exddc/virtualchime/chime/src/webd/web_server.cpp

#include "chime/webd_web_server.h"

#include <algorithm>
#include <array>
#include <cctype>
#include <cerrno>
#include <chrono>
#include <cstdio>
#include <cstring>
#include <ctime>
#include <filesystem>
#include <fstream>
#include <map>
#include <optional>
#include <set>
#include <sstream>
#include <string>
#include <utility>
#include <vector>

#include <arpa/inet.h>
#include <fcntl.h>
#include <netinet/in.h>
#include <sys/socket.h>
#include <sys/stat.h>
#include <unistd.h>

#include <openssl/bn.h>
#include <openssl/err.h>
#include <openssl/pem.h>
#include <openssl/ssl.h>
#include <openssl/x509.h>

#include "chime/webd_apply_manager.h"
#include "chime/webd_config_store.h"
#include "chime/webd_json.h"
#include "chime/webd_string_utils.h"
#include "chime/webd_ui_assets.h"
#include "chime/webd_wifi_scan.h"
#include "vc/config/kv_config.h"
#include "vc/logging/logger.h"

namespace chime::webd {
namespace {

constexpr std::size_t kMaxRequestBytes = 65536;
constexpr std::size_t kMaxBodyBytes = 2 * 1024 * 1024;
constexpr const char *kDefaultRingSoundName = "ring-default.wav";
constexpr const char *kReleaseInfoPath = "/etc/virtualchime-release";
constexpr const char *kAppVersionPath = "/etc/chime-app-version";

bool StartsWith(const std::string &value, const std::string &prefix) {
    return value.size() >= prefix.size() && value.compare(0, prefix.size(), prefix) == 0;
}

std::string MimeTypeOnly(const std::string &content_type) {
    const std::size_t semicolon = content_type.find(';');
    const std::string raw = semicolon == std::string::npos ? content_type : content_type.substr(0, semicolon);
    return ToLower(vc::config::trim(raw));
}

bool IsSafeRelativePath(const std::filesystem::path &path) {
    for (const auto &part : path) {
        if (part == "..") {
            return false;
        }
    }
    return true;
}

bool IsSafeSoundName(const std::string &file_name) {
    if (file_name.empty() || file_name.size() > 128) {
        return false;
    }
    if (file_name.find('/') != std::string::npos || file_name.find('\\') != std::string::npos) {
        return false;
    }
    if (file_name.find("..") != std::string::npos) {
        return false;
    }
    const std::string lowered = ToLower(file_name);
    if (!StartsWith(lowered, "ring-") || lowered.rfind(".wav") != lowered.size() - 4) {
        return false;
    }
    for (const char c : file_name) {
        if (!(std::isalnum(static_cast<unsigned char>(c)) || c == '.' || c == '-' || c == '_')) {
            return false;
        }
    }
    return true;
}

bool EnsureDirectoryExists(const std::string &path, std::string *error) {
    std::error_code ec;
    const bool exists = std::filesystem::exists(path, ec);
    if (ec) {
        if (error != nullptr) {
            *error = "exists(" + path + ") failed: " + ec.message();
        }
        return false;
    }

    if (exists) {
        const bool is_directory = std::filesystem::is_directory(path, ec);
        if (ec) {
            if (error != nullptr) {
                *error = "is_directory(" + path + ") failed: " + ec.message();
            }
            return false;
        }
        if (!is_directory) {
            if (error != nullptr) {
                *error = "path exists but is not a directory: " + path;
            }
            return false;
        }
        return true;
    }

    const bool created = std::filesystem::create_directories(path, ec);
    if (ec) {
        if (error != nullptr) {
            *error = "create_directories(" + path + ") failed: " + ec.message();
        }
        return false;
    }

    (void)created;
    return true;
}

void TrySeedDefaultRingSound(const std::string &ring_sounds_dir, const std::string &active_ring_sound_path,
                             vc::logging::Logger &logger) {
    std::error_code ec;
    const std::filesystem::path source_path(active_ring_sound_path);
    const std::filesystem::path target_path = std::filesystem::path(ring_sounds_dir) / kDefaultRingSoundName;
    const std::filesystem::path temp_path = target_path.string() + ".tmp";

    if (!std::filesystem::exists(source_path, ec)) {
        return;
    }
    if (ec) {
        logger.Warn("webd", "failed to inspect active ring sound: " + source_path.string() + " error=" + ec.message());
        return;
    }
    if (!std::filesystem::is_regular_file(source_path, ec)) {
        return;
    }
    if (ec) {
        logger.Warn("webd", "failed to inspect active ring sound: " + source_path.string() + " error=" + ec.message());
        return;
    }

    if (std::filesystem::exists(target_path, ec)) {
        return;
    }
    if (ec) {
        logger.Warn("webd",
                    "failed to inspect default ring sound target: " + target_path.string() + " error=" + ec.message());
        return;
    }

    std::filesystem::copy_file(source_path, temp_path, std::filesystem::copy_options::overwrite_existing, ec);
    if (ec) {
        logger.Warn("webd", "failed to seed default ring sound: copy " + source_path.string() + " -> " +
                                temp_path.string() + " error=" + ec.message());
        return;
    }

    std::filesystem::rename(temp_path, target_path, ec);
    if (ec) {
        std::error_code remove_ec;
        std::filesystem::remove(temp_path, remove_ec);
        logger.Warn("webd", "failed to seed default ring sound: rename " + temp_path.string() + " -> " +
                                target_path.string() + " error=" + ec.message());
    }
}

std::string ContentTypeForPath(const std::filesystem::path &path) {
    const std::string extension = ToLower(path.extension().string());
    if (extension == ".html") {
        return "text/html; charset=utf-8";
    }
    if (extension == ".css") {
        return "text/css; charset=utf-8";
    }
    if (extension == ".js") {
        return "application/javascript; charset=utf-8";
    }
    if (extension == ".json") {
        return "application/json; charset=utf-8";
    }
    if (extension == ".svg") {
        return "image/svg+xml";
    }
    if (extension == ".ico") {
        return "image/x-icon";
    }
    if (extension == ".png") {
        return "image/png";
    }
    if (extension == ".jpg" || extension == ".jpeg") {
        return "image/jpeg";
    }
    if (extension == ".webp") {
        return "image/webp";
    }
    if (extension == ".woff2") {
        return "font/woff2";
    }
    if (extension == ".woff") {
        return "font/woff";
    }
    return "application/octet-stream";
}

std::string CacheControlForPath(const std::string &request_path, const std::filesystem::path &path) {
    if (ToLower(path.extension().string()) == ".html") {
        return "no-cache";
    }
    if (StartsWith(request_path, "/assets/")) {
        return "public, max-age=31536000, immutable";
    }
    return "public, max-age=3600";
}

bool ReadFile(const std::filesystem::path &path, std::string *body) {
    if (body == nullptr) {
        return false;
    }
    std::ifstream file(path, std::ios::binary);
    if (!file.is_open()) {
        return false;
    }
    std::ostringstream stream;
    stream << file.rdbuf();
    *body = stream.str();
    return true;
}

std::vector<std::string> ReadObservedTopicsFromFile(const std::string &path, std::string *error) {
    std::vector<std::string> topics;
    std::ifstream file(path);
    if (!file.is_open()) {
        if (std::filesystem::exists(path)) {
            if (error != nullptr) {
                *error = "failed to open observed topics file";
            }
        }
        return topics;
    }

    std::set<std::string> seen;
    std::string line;
    while (std::getline(file, line)) {
        const std::string topic = vc::config::trim(line);
        if (topic.empty()) {
            continue;
        }
        if (seen.insert(topic).second) {
            topics.push_back(topic);
        }
    }
    return topics;
}

std::string ReadTrimmedFirstLine(const std::string &path) {
    std::ifstream file(path);
    if (!file.is_open()) {
        return "";
    }
    std::string line;
    if (!std::getline(file, line)) {
        return "";
    }
    return vc::config::trim(line);
}

std::map<std::string, std::string> ReadKeyValueFile(const std::string &path) {
    std::map<std::string, std::string> values;
    std::ifstream file(path);
    if (!file.is_open()) {
        return values;
    }

    std::string line;
    while (std::getline(file, line)) {
        const std::string trimmed = vc::config::trim(line);
        if (trimmed.empty() || trimmed[0] == '#') {
            continue;
        }

        const std::size_t separator = trimmed.find('=');
        if (separator == std::string::npos) {
            continue;
        }

        const std::string key = vc::config::trim(trimmed.substr(0, separator));
        const std::string value = vc::config::trim(trimmed.substr(separator + 1));
        if (!key.empty()) {
            values[key] = value;
        }
    }

    return values;
}

std::string ReadValueOrDefault(const std::map<std::string, std::string> &values, const std::string &key,
                               const std::string &fallback) {
    const auto it = values.find(key);
    if (it == values.end() || it->second.empty()) {
        return fallback;
    }
    return it->second;
}

std::string StatusText(int code) {
    switch (code) {
    case 200:
        return "OK";
    case 400:
        return "Bad Request";
    case 404:
        return "Not Found";
    case 405:
        return "Method Not Allowed";
    case 500:
        return "Internal Server Error";
    case 501:
        return "Not Implemented";
    case 503:
        return "Service Unavailable";
    default:
        return "Error";
    }
}

bool WriteAllSsl(SSL *ssl, const std::string &data) {
    std::size_t offset = 0;
    while (offset < data.size()) {
        const int written =
            SSL_write(ssl, data.data() + offset, static_cast<int>(std::min<std::size_t>(data.size() - offset, 16384)));
        if (written <= 0) {
            return false;
        }
        offset += static_cast<std::size_t>(written);
    }
    return true;
}

std::optional<std::string> ReadRequiredString(const JsonValue &object, const std::string &key,
                                              std::vector<ValidationError> *errors) {
    const auto field = GetObjectField(object, key);
    if (!field.has_value()) {
        if (errors != nullptr) {
            errors->push_back({key, key + " is required"});
        }
        return std::nullopt;
    }

    std::string value;
    if (!field->AsString(&value)) {
        if (errors != nullptr) {
            errors->push_back({key, key + " must be a string"});
        }
        return std::nullopt;
    }

    return value;
}

std::optional<int> ReadRequiredInt(const JsonValue &object, const std::string &key,
                                   std::vector<ValidationError> *errors) {
    const auto field = GetObjectField(object, key);
    if (!field.has_value()) {
        if (errors != nullptr) {
            errors->push_back({key, key + " is required"});
        }
        return std::nullopt;
    }

    double value = 0.0;
    if (!field->AsNumber(&value)) {
        if (errors != nullptr) {
            errors->push_back({key, key + " must be a number"});
        }
        return std::nullopt;
    }

    const int rounded = static_cast<int>(value);
    if (static_cast<double>(rounded) != value) {
        if (errors != nullptr) {
            errors->push_back({key, key + " must be an integer"});
        }
        return std::nullopt;
    }

    return rounded;
}

std::optional<bool> ReadRequiredBool(const JsonValue &object, const std::string &key,
                                     std::vector<ValidationError> *errors) {
    const auto field = GetObjectField(object, key);
    if (!field.has_value()) {
        if (errors != nullptr) {
            errors->push_back({key, key + " is required"});
        }
        return std::nullopt;
    }

    bool value = false;
    if (!field->AsBool(&value)) {
        if (errors != nullptr) {
            errors->push_back({key, key + " must be a boolean"});
        }
        return std::nullopt;
    }

    return value;
}

std::optional<std::vector<std::string>> ReadRequiredStringArray(const JsonValue &object, const std::string &key,
                                                                std::vector<ValidationError> *errors) {
    const auto field = GetObjectField(object, key);
    if (!field.has_value()) {
        if (errors != nullptr) {
            errors->push_back({key, key + " is required"});
        }
        return std::nullopt;
    }

    std::vector<JsonValue> items;
    if (!field->AsArray(&items)) {
        if (errors != nullptr) {
            errors->push_back({key, key + " must be an array"});
        }
        return std::nullopt;
    }

    std::vector<std::string> output;
    output.reserve(items.size());
    for (std::size_t i = 0; i < items.size(); ++i) {
        std::string entry;
        if (!items[i].AsString(&entry)) {
            if (errors != nullptr) {
                errors->push_back({key, key + "[" + std::to_string(i) + "] must be a string"});
            }
            continue;
        }
        output.push_back(entry);
    }

    return output;
}

std::optional<std::string> ReadOptionalString(const JsonValue &object, const std::string &key,
                                              std::vector<ValidationError> *errors) {
    const auto field = GetObjectField(object, key);
    if (!field.has_value()) {
        return std::nullopt;
    }

    std::string value;
    if (!field->AsString(&value)) {
        if (errors != nullptr) {
            errors->push_back({key, key + " must be a string"});
        }
        return std::nullopt;
    }

    return value;
}

std::string SerializeValidationErrors(const std::vector<ValidationError> &validation_errors) {
    std::string body = "[";
    for (std::size_t i = 0; i < validation_errors.size(); ++i) {
        if (i > 0) {
            body += ",";
        }
        body += "{";
        body += "\"field\":" + JsonString(validation_errors[i].field) + ",";
        body += "\"message\":" + JsonString(validation_errors[i].message);
        body += "}";
    }
    body += "]";
    return body;
}

std::string SerializeTopics(const std::vector<std::string> &topics) {
    std::string output = "[";
    for (std::size_t i = 0; i < topics.size(); ++i) {
        if (i > 0) {
            output += ",";
        }
        output += JsonString(topics[i]);
    }
    output += "]";
    return output;
}

std::string SerializeApplyStatus(const ApplyStatus &status) {
    std::string output = "{";
    output += "\"job_id\":" + std::to_string(status.job_id) + ",";
    output += "\"state\":" + JsonString(status.state) + ",";
    output += "\"started_at_utc\":" + JsonString(status.started_at_utc) + ",";
    output += "\"finished_at_utc\":" + JsonString(status.finished_at_utc) + ",";
    output += "\"error\":" + JsonString(status.error);
    output += "}";
    return output;
}

bool GenerateSelfSignedCertificate(const std::string &cert_path, const std::string &key_path, std::string *error) {
    EVP_PKEY *pkey = EVP_PKEY_new();
    if (pkey == nullptr) {
        if (error != nullptr) {
            *error = "EVP_PKEY_new failed";
        }
        return false;
    }

    RSA *rsa = RSA_new();
    BIGNUM *exponent = BN_new();
    X509 *cert = nullptr;
    X509_NAME *name = nullptr;
    FILE *key_file = nullptr;
    FILE *cert_file = nullptr;

    bool success = false;

    if (rsa == nullptr || exponent == nullptr) {
        if (error != nullptr) {
            *error = "RSA allocation failed";
        }
        goto cleanup;
    }

    if (BN_set_word(exponent, RSA_F4) != 1) {
        if (error != nullptr) {
            *error = "BN_set_word failed";
        }
        goto cleanup;
    }

    if (RSA_generate_key_ex(rsa, 2048, exponent, nullptr) != 1) {
        if (error != nullptr) {
            *error = "RSA_generate_key_ex failed";
        }
        goto cleanup;
    }

    if (EVP_PKEY_assign_RSA(pkey, rsa) != 1) {
        if (error != nullptr) {
            *error = "EVP_PKEY_assign_RSA failed";
        }
        goto cleanup;
    }
    rsa = nullptr;

    cert = X509_new();
    if (cert == nullptr) {
        if (error != nullptr) {
            *error = "X509_new failed";
        }
        goto cleanup;
    }

    X509_set_version(cert, 2);
    ASN1_INTEGER_set(X509_get_serialNumber(cert), static_cast<long>(time(nullptr)));
    X509_gmtime_adj(X509_get_notBefore(cert), 0);
    X509_gmtime_adj(X509_get_notAfter(cert), 60L * 60L * 24L * 365L * 10L);
    X509_set_pubkey(cert, pkey);

    name = X509_get_subject_name(cert);
    X509_NAME_add_entry_by_txt(name, "C", MBSTRING_ASC, reinterpret_cast<const unsigned char *>("US"), -1, -1, 0);
    X509_NAME_add_entry_by_txt(name, "O", MBSTRING_ASC, reinterpret_cast<const unsigned char *>("VirtualChime"), -1, -1,
                               0);
    X509_NAME_add_entry_by_txt(name, "CN", MBSTRING_ASC, reinterpret_cast<const unsigned char *>("chime.local"), -1, -1,
                               0);
    X509_set_issuer_name(cert, name);

    if (X509_sign(cert, pkey, EVP_sha256()) == 0) {
        if (error != nullptr) {
            *error = "X509_sign failed";
        }
        goto cleanup;
    }

    key_file = fopen(key_path.c_str(), "w");
    if (key_file == nullptr) {
        if (error != nullptr) {
            *error = "failed to open key file";
        }
        goto cleanup;
    }
    if (PEM_write_PrivateKey(key_file, pkey, nullptr, nullptr, 0, nullptr, nullptr) != 1) {
        if (error != nullptr) {
            *error = "PEM_write_PrivateKey failed";
        }
        goto cleanup;
    }

    cert_file = fopen(cert_path.c_str(), "w");
    if (cert_file == nullptr) {
        if (error != nullptr) {
            *error = "failed to open cert file";
        }
        goto cleanup;
    }
    if (PEM_write_X509(cert_file, cert) != 1) {
        if (error != nullptr) {
            *error = "PEM_write_X509 failed";
        }
        goto cleanup;
    }

    chmod(key_path.c_str(), 0600);
    chmod(cert_path.c_str(), 0644);
    success = true;

cleanup:
    if (key_file != nullptr) {
        fclose(key_file);
    }
    if (cert_file != nullptr) {
        fclose(cert_file);
    }
    if (rsa != nullptr) {
        RSA_free(rsa);
    }
    if (exponent != nullptr) {
        BN_free(exponent);
    }
    if (cert != nullptr) {
        X509_free(cert);
    }
    EVP_PKEY_free(pkey);

    return success;
}

} // namespace

WebServer::WebServer(vc::logging::Logger &logger, ConfigStore &config_store, WifiScanner &wifi_scanner,
                     ApplyManager &apply_manager, std::string bind_address, int port, std::string cert_path,
                     std::string key_path, std::string ui_dist_dir, std::string observed_topics_path,
                     std::string ring_sounds_dir, std::string active_ring_sound_path)
    : logger_(logger), config_store_(config_store), wifi_scanner_(wifi_scanner), apply_manager_(apply_manager),
      bind_address_(std::move(bind_address)), port_(port), cert_path_(std::move(cert_path)),
      key_path_(std::move(key_path)), ui_dist_dir_(std::move(ui_dist_dir)),
      observed_topics_path_(std::move(observed_topics_path)), ring_sounds_dir_(std::move(ring_sounds_dir)),
      active_ring_sound_path_(std::move(active_ring_sound_path)) {}

WebServer::~WebServer() {
    Stop();
}

bool WebServer::Start() {
    if (running_.load()) {
        return true;
    }

    std::string error;
    if (!EnsureTlsMaterial(&error)) {
        logger_.Error("webd", "TLS setup failed: " + error);
        return false;
    }

    SSL_load_error_strings();
    OpenSSL_add_ssl_algorithms();

    SSL_CTX *ctx = SSL_CTX_new(TLS_server_method());
    if (ctx == nullptr) {
        logger_.Error("webd", "SSL_CTX_new failed");
        return false;
    }

    SSL_CTX_set_min_proto_version(ctx, TLS1_2_VERSION);

    if (SSL_CTX_use_certificate_file(ctx, cert_path_.c_str(), SSL_FILETYPE_PEM) != 1) {
        logger_.Error("webd", "failed to load TLS certificate from " + cert_path_);
        SSL_CTX_free(ctx);
        return false;
    }

    if (SSL_CTX_use_PrivateKey_file(ctx, key_path_.c_str(), SSL_FILETYPE_PEM) != 1) {
        logger_.Error("webd", "failed to load TLS private key from " + key_path_);
        SSL_CTX_free(ctx);
        return false;
    }

    listen_fd_ = socket(AF_INET, SOCK_STREAM, 0);
    if (listen_fd_ < 0) {
        logger_.Error("webd", "socket() failed");
        SSL_CTX_free(ctx);
        return false;
    }

    const int reuse = 1;
    setsockopt(listen_fd_, SOL_SOCKET, SO_REUSEADDR, &reuse, sizeof(reuse));

    struct sockaddr_in address{};
    address.sin_family = AF_INET;
    address.sin_port = htons(static_cast<uint16_t>(port_));
    if (inet_pton(AF_INET, bind_address_.c_str(), &address.sin_addr) != 1) {
        logger_.Error("webd", "invalid bind address: " + bind_address_);
        close(listen_fd_);
        listen_fd_ = -1;
        SSL_CTX_free(ctx);
        return false;
    }

    if (bind(listen_fd_, reinterpret_cast<struct sockaddr *>(&address), sizeof(address)) != 0) {
        logger_.Error("webd", "bind() failed on " + bind_address_ + ":" + std::to_string(port_));
        close(listen_fd_);
        listen_fd_ = -1;
        SSL_CTX_free(ctx);
        return false;
    }

    if (listen(listen_fd_, 16) != 0) {
        logger_.Error("webd", "listen() failed");
        close(listen_fd_);
        listen_fd_ = -1;
        SSL_CTX_free(ctx);
        return false;
    }

    ssl_ctx_ = ctx;
    running_.store(true);
    accept_thread_ = std::thread([this]() { AcceptLoop(); });

    logger_.Info("webd", "https server listening on " + bind_address_ + ":" + std::to_string(port_));
    return true;
}

void WebServer::Stop() {
    if (!running_.exchange(false)) {
        return;
    }

    if (listen_fd_ >= 0) {
        shutdown(listen_fd_, SHUT_RDWR);
        close(listen_fd_);
        listen_fd_ = -1;
    }

    if (accept_thread_.joinable()) {
        accept_thread_.join();
    }

    if (ssl_ctx_ != nullptr) {
        SSL_CTX_free(static_cast<SSL_CTX *>(ssl_ctx_));
        ssl_ctx_ = nullptr;
    }

    EVP_cleanup();
}

void WebServer::AcceptLoop() {
    while (running_.load()) {
        struct sockaddr_in client_addr{};
        socklen_t client_len = sizeof(client_addr);
        const int client_fd = accept(listen_fd_, reinterpret_cast<struct sockaddr *>(&client_addr), &client_len);

        if (client_fd < 0) {
            if (errno == EINTR) {
                continue;
            }
            if (!running_.load()) {
                break;
            }
            std::this_thread::sleep_for(std::chrono::milliseconds(50));
            continue;
        }

        HandleConnection(client_fd);
    }
}

void WebServer::HandleConnection(int client_fd) {
    SSL *ssl = SSL_new(static_cast<SSL_CTX *>(ssl_ctx_));
    if (ssl == nullptr) {
        close(client_fd);
        return;
    }

    SSL_set_fd(ssl, client_fd);
    if (SSL_accept(ssl) <= 0) {
        SSL_shutdown(ssl);
        SSL_free(ssl);
        close(client_fd);
        return;
    }

    HttpRequest request;
    std::string read_error;
    HttpResponse response;
    if (!ReadHttpRequest(ssl, &request, &read_error)) {
        response.status = 400;
        response.body = "{\"error\":\"bad_request\",\"message\":" + JsonString(read_error) + "}";
    } else {
        response = Route(request);
    }

    std::string raw;
    raw += "HTTP/1.1 " + std::to_string(response.status) + " " + StatusText(response.status) + "\r\n";
    raw += "Content-Type: " + response.content_type + "\r\n";
    raw += "Content-Length: " + std::to_string(response.body.size()) + "\r\n";
    raw += "Cache-Control: " + response.cache_control + "\r\n";
    raw += "Connection: close\r\n";
    raw += "\r\n";
    raw += response.body;

    WriteAllSsl(ssl, raw);

    SSL_shutdown(ssl);
    SSL_free(ssl);
    close(client_fd);
}

bool WebServer::ReadHttpRequest(void *ssl_ptr, HttpRequest *request, std::string *error) const {
    if (ssl_ptr == nullptr || request == nullptr || error == nullptr) {
        return false;
    }

    SSL *ssl = static_cast<SSL *>(ssl_ptr);

    std::string data;
    data.reserve(2048);

    std::size_t headers_end = std::string::npos;
    while (headers_end == std::string::npos) {
        if (data.size() >= kMaxRequestBytes) {
            *error = "request too large";
            return false;
        }

        std::array<char, 2048> buffer{};
        const int bytes = SSL_read(ssl, buffer.data(), static_cast<int>(buffer.size()));
        if (bytes <= 0) {
            *error = "failed to read request";
            return false;
        }

        data.append(buffer.data(), static_cast<std::size_t>(bytes));
        headers_end = data.find("\r\n\r\n");
    }

    const std::string header_blob = data.substr(0, headers_end);
    std::istringstream header_stream(header_blob);

    std::string request_line;
    if (!std::getline(header_stream, request_line)) {
        *error = "missing request line";
        return false;
    }
    if (!request_line.empty() && request_line.back() == '\r') {
        request_line.pop_back();
    }

    std::istringstream request_line_stream(request_line);
    std::string method;
    std::string path;
    std::string version;
    request_line_stream >> method >> path >> version;
    if (method.empty() || path.empty() || version.empty()) {
        *error = "invalid request line";
        return false;
    }

    std::map<std::string, std::string> headers;
    std::string header_line;
    while (std::getline(header_stream, header_line)) {
        if (!header_line.empty() && header_line.back() == '\r') {
            header_line.pop_back();
        }
        const auto sep = header_line.find(':');
        if (sep == std::string::npos) {
            continue;
        }
        const std::string key = ToLower(vc::config::trim(header_line.substr(0, sep)));
        const std::string value = vc::config::trim(header_line.substr(sep + 1));
        headers[key] = value;
    }

    std::size_t content_length = 0;
    const auto content_length_it = headers.find("content-length");
    if (content_length_it != headers.end()) {
        char *end = nullptr;
        const long parsed = std::strtol(content_length_it->second.c_str(), &end, 10);
        if (end == nullptr || *end != '\0' || parsed < 0) {
            *error = "invalid Content-Length";
            return false;
        }
        content_length = static_cast<std::size_t>(parsed);
    }

    if (content_length > kMaxBodyBytes) {
        *error = "request body too large";
        return false;
    }

    std::string body = data.substr(headers_end + 4);
    while (body.size() < content_length) {
        std::array<char, 2048> buffer{};
        const int bytes = SSL_read(ssl, buffer.data(), static_cast<int>(buffer.size()));
        if (bytes <= 0) {
            *error = "failed to read request body";
            return false;
        }
        body.append(buffer.data(), static_cast<std::size_t>(bytes));
        if (body.size() > kMaxBodyBytes) {
            *error = "request body too large";
            return false;
        }
    }

    if (body.size() > content_length) {
        body.resize(content_length);
    }

    const auto query = path.find('?');
    if (query != std::string::npos) {
        path = path.substr(0, query);
    }

    request->method = method;
    request->path = path;
    request->body = std::move(body);
    const auto content_type_it = headers.find("content-type");
    request->has_content_type = content_type_it != headers.end();
    request->content_type = content_type_it != headers.end() ? content_type_it->second : "";
    return true;
}

WebServer::HttpResponse WebServer::Route(const HttpRequest &request) {
    if (request.path == "/api/v1/config/core") {
        if (request.method == "GET") {
            return HandleGetCoreConfig();
        }
        if (request.method == "POST") {
            return HandlePostCoreConfig(request);
        }
        HttpResponse response;
        response.status = 405;
        response.body = "{\"error\":\"method_not_allowed\"}";
        return response;
    }

    if (request.path == "/api/v1/wifi/scan") {
        if (request.method != "GET") {
            HttpResponse response;
            response.status = 405;
            response.body = "{\"error\":\"method_not_allowed\"}";
            return response;
        }
        return HandleWifiScan();
    }

    if (request.path == "/api/v1/system/version") {
        if (request.method != "GET") {
            HttpResponse response;
            response.status = 405;
            response.body = "{\"error\":\"method_not_allowed\"}";
            return response;
        }
        return HandleGetSystemVersion();
    }

    if (request.path == "/api/v1/mqtt/topics") {
        if (request.method != "GET") {
            HttpResponse response;
            response.status = 405;
            response.body = "{\"error\":\"method_not_allowed\"}";
            return response;
        }
        return HandleGetObservedTopics();
    }

    if (request.path == "/api/v1/ring/sounds") {
        if (request.method == "GET") {
            return HandleGetRingSounds();
        }
        HttpResponse response;
        response.status = 405;
        response.body = "{\"error\":\"method_not_allowed\"}";
        return response;
    }

    if (request.path.rfind("/api/v1/ring/sounds/", 0) == 0) {
        if (request.path == "/api/v1/ring/sounds/select") {
            if (request.method != "POST") {
                HttpResponse response;
                response.status = 405;
                response.body = "{\"error\":\"method_not_allowed\"}";
                return response;
            }
            return HandleSelectRingSound(request);
        }

        if (request.method != "PUT") {
            HttpResponse response;
            response.status = 405;
            response.body = "{\"error\":\"method_not_allowed\"}";
            return response;
        }
        return HandleUploadRingSound(request);
    }

    if (request.path == "/api/v1/system" || request.path == "/api/v1/device" || request.path == "/api/v1/diagnostics" ||
        request.path.rfind("/api/v1/system/", 0) == 0 || request.path.rfind("/api/v1/device/", 0) == 0 ||
        request.path.rfind("/api/v1/diagnostics/", 0) == 0) {
        return ReservedNotImplemented(request.path);
    }

    if (const auto ui_response = TryServeExternalUi(request); ui_response.has_value()) {
        return *ui_response;
    }

    if (request.method == "GET" && request.path == "/") {
        HttpResponse response;
        response.status = 200;
        response.content_type = "text/html; charset=utf-8";
        response.body = MainPageHtml();
        return response;
    }

    HttpResponse response;
    response.status = 404;
    response.body = "{\"error\":\"not_found\"}";
    return response;
}

WebServer::HttpResponse WebServer::HandleGetCoreConfig() {
    const SaveResult loaded = config_store_.LoadCoreConfig();
    HttpResponse response;
    if (!loaded.success) {
        response.status = 500;
        response.body = "{\"error\":\"load_failed\",\"message\":" + JsonString(loaded.error) + "}";
        return response;
    }

    response.status = 200;
    response.body = "{";
    response.body += "\"wifi_ssid\":" + JsonString(loaded.snapshot.config.wifi_ssid) + ",";
    response.body += "\"wifi_password_set\":" + JsonBool(loaded.snapshot.wifi_password_set) + ",";
    response.body += "\"mqtt_host\":" + JsonString(loaded.snapshot.config.mqtt_host) + ",";
    response.body += "\"mqtt_port\":" + JsonNumber(loaded.snapshot.config.mqtt_port) + ",";
    response.body += "\"mqtt_client_id\":" + JsonString(loaded.snapshot.config.mqtt_client_id) + ",";
    response.body += "\"mqtt_username\":" + JsonString(loaded.snapshot.config.mqtt_username) + ",";
    response.body += "\"mqtt_password_set\":" + JsonBool(loaded.snapshot.mqtt_password_set) + ",";
    response.body += "\"mqtt_tls_enabled\":" + JsonBool(loaded.snapshot.config.mqtt_tls_enabled) + ",";
    response.body +=
        "\"mqtt_tls_validate_certificate\":" + JsonBool(loaded.snapshot.config.mqtt_tls_validate_certificate) + ",";
    response.body += "\"mqtt_tls_ca_file\":" + JsonString(loaded.snapshot.config.mqtt_tls_ca_file) + ",";
    response.body += "\"mqtt_tls_cert_file\":" + JsonString(loaded.snapshot.config.mqtt_tls_cert_file) + ",";
    response.body += "\"mqtt_tls_key_file\":" + JsonString(loaded.snapshot.config.mqtt_tls_key_file) + ",";
    response.body += "\"mqtt_topics\":" + SerializeTopics(loaded.snapshot.config.mqtt_topics) + ",";
    response.body += "\"ring_topic\":" + JsonString(loaded.snapshot.config.ring_topic) + ",";
    response.body += "\"notification_success_sound_path\":" +
                     JsonString(loaded.snapshot.config.notification_success_sound_path) + ",";
    response.body += "\"notification_failure_sound_path\":" +
                     JsonString(loaded.snapshot.config.notification_failure_sound_path) + ",";
    response.body += "\"volume_bell\":" + JsonNumber(loaded.snapshot.config.volume_bell) + ",";
    response.body += "\"volume_notifications\":" + JsonNumber(loaded.snapshot.config.volume_notifications) + ",";
    response.body += "\"volume_other\":" + JsonNumber(loaded.snapshot.config.volume_other) + ",";
    response.body += "\"apply\":" + SerializeApplyStatus(apply_manager_.CurrentStatus());
    response.body += "}";
    return response;
}

WebServer::HttpResponse WebServer::HandlePostCoreConfig(const HttpRequest &request) {
    HttpResponse response;

    const JsonParseResult parsed = ParseJson(request.body);
    if (!parsed.success) {
        response.status = 400;
        response.body = "{\"error\":\"invalid_json\",\"message\":" + JsonString(parsed.error) + "}";
        return response;
    }

    if (parsed.value.type() != JsonValue::Type::kObject) {
        response.status = 400;
        response.body = "{\"error\":\"invalid_payload\",\"message\":\"payload must be an object\"}";
        return response;
    }

    std::vector<ValidationError> parse_errors;

    SaveRequest save_request;

    const auto wifi_ssid = ReadRequiredString(parsed.value, "wifi_ssid", &parse_errors);
    const auto mqtt_host = ReadRequiredString(parsed.value, "mqtt_host", &parse_errors);
    const auto mqtt_port = ReadRequiredInt(parsed.value, "mqtt_port", &parse_errors);
    const auto mqtt_client_id = ReadRequiredString(parsed.value, "mqtt_client_id", &parse_errors);
    const auto mqtt_username = ReadRequiredString(parsed.value, "mqtt_username", &parse_errors);
    const auto mqtt_tls_enabled = ReadRequiredBool(parsed.value, "mqtt_tls_enabled", &parse_errors);
    const auto mqtt_tls_validate_certificate =
        ReadRequiredBool(parsed.value, "mqtt_tls_validate_certificate", &parse_errors);
    const auto mqtt_tls_ca_file = ReadRequiredString(parsed.value, "mqtt_tls_ca_file", &parse_errors);
    const auto mqtt_tls_cert_file = ReadRequiredString(parsed.value, "mqtt_tls_cert_file", &parse_errors);
    const auto mqtt_tls_key_file = ReadRequiredString(parsed.value, "mqtt_tls_key_file", &parse_errors);
    const auto mqtt_topics = ReadRequiredStringArray(parsed.value, "mqtt_topics", &parse_errors);
    const auto ring_topic = ReadRequiredString(parsed.value, "ring_topic", &parse_errors);
    const auto notification_success_sound_path =
        ReadOptionalString(parsed.value, "notification_success_sound_path", &parse_errors);
    const auto notification_failure_sound_path =
        ReadOptionalString(parsed.value, "notification_failure_sound_path", &parse_errors);
    const auto volume_bell = ReadRequiredInt(parsed.value, "volume_bell", &parse_errors);
    const auto volume_notifications = ReadRequiredInt(parsed.value, "volume_notifications", &parse_errors);
    const auto volume_other = ReadRequiredInt(parsed.value, "volume_other", &parse_errors);
    const auto wifi_password = ReadOptionalString(parsed.value, "wifi_password", &parse_errors);
    const auto mqtt_password = ReadOptionalString(parsed.value, "mqtt_password", &parse_errors);

    if (!parse_errors.empty()) {
        response.status = 400;
        response.body = "{";
        response.body += "\"error\":\"validation_failed\",";
        response.body += "\"validation_errors\":" + SerializeValidationErrors(parse_errors);
        response.body += "}";
        return response;
    }

    std::optional<CoreConfigSnapshot> existing_snapshot;
    if (!notification_success_sound_path.has_value() ||
        !notification_failure_sound_path.has_value()) {
        const SaveResult loaded = config_store_.LoadCoreConfig();
        if (!loaded.success) {
            response.status = 500;
            response.body = "{\"error\":\"save_failed\",\"message\":" + JsonString(loaded.error) + "}";
            return response;
        }
        existing_snapshot = loaded.snapshot;
    }

    save_request.config.wifi_ssid = *wifi_ssid;
    save_request.config.mqtt_host = *mqtt_host;
    save_request.config.mqtt_port = *mqtt_port;
    save_request.config.mqtt_client_id = *mqtt_client_id;
    save_request.config.mqtt_username = *mqtt_username;
    save_request.config.mqtt_tls_enabled = *mqtt_tls_enabled;
    save_request.config.mqtt_tls_validate_certificate = *mqtt_tls_validate_certificate;
    save_request.config.mqtt_tls_ca_file = *mqtt_tls_ca_file;
    save_request.config.mqtt_tls_cert_file = *mqtt_tls_cert_file;
    save_request.config.mqtt_tls_key_file = *mqtt_tls_key_file;
    save_request.config.mqtt_topics = *mqtt_topics;
    save_request.config.ring_topic = *ring_topic;
    if (notification_success_sound_path.has_value()) {
        save_request.config.notification_success_sound_path = *notification_success_sound_path;
    } else if (existing_snapshot.has_value()) {
        save_request.config.notification_success_sound_path =
            existing_snapshot->config.notification_success_sound_path;
    }
    if (notification_failure_sound_path.has_value()) {
        save_request.config.notification_failure_sound_path = *notification_failure_sound_path;
    } else if (existing_snapshot.has_value()) {
        save_request.config.notification_failure_sound_path =
            existing_snapshot->config.notification_failure_sound_path;
    }
    save_request.config.volume_bell = *volume_bell;
    save_request.config.volume_notifications = *volume_notifications;
    save_request.config.volume_other = *volume_other;
    save_request.wifi_password = wifi_password;
    save_request.mqtt_password = mqtt_password;

    const SaveResult saved = config_store_.SaveCoreConfig(save_request);
    if (!saved.validation_errors.empty()) {
        response.status = 400;
        response.body = "{";
        response.body += "\"error\":\"validation_failed\",";
        response.body += "\"validation_errors\":" + SerializeValidationErrors(saved.validation_errors);
        response.body += "}";
        return response;
    }

    if (!saved.success) {
        response.status = 500;
        response.body = "{\"error\":\"save_failed\",\"message\":" + JsonString(saved.error) + "}";
        return response;
    }

    const ApplyStatus apply = apply_manager_.StartApply();

    response.status = 200;
    response.body = "{";
    response.body += "\"wifi_ssid\":" + JsonString(saved.snapshot.config.wifi_ssid) + ",";
    response.body += "\"wifi_password_set\":" + JsonBool(saved.snapshot.wifi_password_set) + ",";
    response.body += "\"mqtt_host\":" + JsonString(saved.snapshot.config.mqtt_host) + ",";
    response.body += "\"mqtt_port\":" + JsonNumber(saved.snapshot.config.mqtt_port) + ",";
    response.body += "\"mqtt_client_id\":" + JsonString(saved.snapshot.config.mqtt_client_id) + ",";
    response.body += "\"mqtt_username\":" + JsonString(saved.snapshot.config.mqtt_username) + ",";
    response.body += "\"mqtt_password_set\":" + JsonBool(saved.snapshot.mqtt_password_set) + ",";
    response.body += "\"mqtt_tls_enabled\":" + JsonBool(saved.snapshot.config.mqtt_tls_enabled) + ",";
    response.body +=
        "\"mqtt_tls_validate_certificate\":" + JsonBool(saved.snapshot.config.mqtt_tls_validate_certificate) + ",";
    response.body += "\"mqtt_tls_ca_file\":" + JsonString(saved.snapshot.config.mqtt_tls_ca_file) + ",";
    response.body += "\"mqtt_tls_cert_file\":" + JsonString(saved.snapshot.config.mqtt_tls_cert_file) + ",";
    response.body += "\"mqtt_tls_key_file\":" + JsonString(saved.snapshot.config.mqtt_tls_key_file) + ",";
    response.body += "\"mqtt_topics\":" + SerializeTopics(saved.snapshot.config.mqtt_topics) + ",";
    response.body += "\"ring_topic\":" + JsonString(saved.snapshot.config.ring_topic) + ",";
    response.body += "\"notification_success_sound_path\":" +
                     JsonString(saved.snapshot.config.notification_success_sound_path) + ",";
    response.body += "\"notification_failure_sound_path\":" +
                     JsonString(saved.snapshot.config.notification_failure_sound_path) + ",";
    response.body += "\"volume_bell\":" + JsonNumber(saved.snapshot.config.volume_bell) + ",";
    response.body += "\"volume_notifications\":" + JsonNumber(saved.snapshot.config.volume_notifications) + ",";
    response.body += "\"volume_other\":" + JsonNumber(saved.snapshot.config.volume_other) + ",";
    response.body += "\"apply\":" + SerializeApplyStatus(apply);
    response.body += "}";

    return response;
}

WebServer::HttpResponse WebServer::HandleWifiScan() {
    const WifiScanResult scan = wifi_scanner_.Scan();
    HttpResponse response;
    if (!scan.success) {
        response.status = 503;
        response.body = "{\"error\":\"scan_failed\",\"message\":" + JsonString(scan.error) + "}";
        return response;
    }

    response.status = 200;
    response.body = "{";
    response.body += "\"networks\":[";
    for (std::size_t i = 0; i < scan.networks.size(); ++i) {
        if (i > 0) {
            response.body += ",";
        }
        response.body += "{";
        response.body += "\"ssid\":" + JsonString(scan.networks[i].ssid) + ",";
        response.body += "\"signal_dbm\":" + JsonNumber(scan.networks[i].signal_dbm) + ",";
        response.body += "\"security\":" + JsonString(scan.networks[i].security);
        response.body += "}";
    }
    response.body += "]";
    response.body += "}";

    return response;
}

WebServer::HttpResponse WebServer::HandleGetSystemVersion() {
    HttpResponse response;
    const std::map<std::string, std::string> release_values = ReadKeyValueFile(kReleaseInfoPath);

    const std::string chime_version_fallback = ReadValueOrDefault(
        release_values, "CHIME_APP_VERSION_FULL", ReadValueOrDefault(release_values, "CHIME_APP_VERSION", "unknown"));
    const std::string chime_version = [&]() {
        const std::string app_version_file = ReadTrimmedFirstLine(kAppVersionPath);
        if (!app_version_file.empty()) {
            return app_version_file;
        }
        return chime_version_fallback;
    }();

    const std::string os_version =
        ReadValueOrDefault(release_values, "VIRTUALCHIME_OS_VERSION_FULL",
                           ReadValueOrDefault(release_values, "VIRTUALCHIME_OS_VERSION", "unknown"));
    const std::string config_version = ReadValueOrDefault(release_values, "CHIME_CONFIG_VERSION", "unknown");

    response.status = 200;
    response.body = "{";
    response.body += "\"chime_version\":" + JsonString(chime_version) + ",";
    response.body += "\"os_version\":" + JsonString(os_version) + ",";
    response.body += "\"config_version\":" + JsonString(config_version);
    response.body += "}";
    return response;
}

WebServer::HttpResponse WebServer::HandleGetObservedTopics() {
    HttpResponse response;
    std::string read_error;
    const std::vector<std::string> topics = ReadObservedTopicsFromFile(observed_topics_path_, &read_error);

    if (!read_error.empty()) {
        logger_.Warn("webd", read_error + " path=" + observed_topics_path_);
    }

    response.status = 200;
    response.body = "{";
    response.body += "\"topics\":" + SerializeTopics(topics);
    response.body += "}";
    return response;
}

WebServer::HttpResponse WebServer::HandleGetRingSounds() {
    HttpResponse response;

    std::string ensure_error;
    if (!EnsureDirectoryExists(ring_sounds_dir_, &ensure_error)) {
        response.status = 500;
        response.body = "{\"error\":\"ring_sounds_unavailable\",\"message\":" + JsonString(ensure_error) + "}";
        return response;
    }

    TrySeedDefaultRingSound(ring_sounds_dir_, active_ring_sound_path_, logger_);

    const std::string selected_path = ring_sounds_dir_ + "/selected.txt";
    std::string selected_name;
    {
        std::ifstream selected_file(selected_path);
        if (selected_file.is_open()) {
            std::getline(selected_file, selected_name);
            selected_name = vc::config::trim(selected_name);
        }
    }

    std::vector<std::string> sounds;
    std::error_code ec;
    for (const auto &entry : std::filesystem::directory_iterator(ring_sounds_dir_, ec)) {
        if (ec) {
            break;
        }
        if (!entry.is_regular_file(ec)) {
            continue;
        }
        const std::string name = entry.path().filename().string();
        if (!IsSafeSoundName(name)) {
            continue;
        }
        sounds.push_back(name);
    }

    if (ec) {
        logger_.Warn("webd", "failed to iterate ring sounds directory: " + ring_sounds_dir_ + " error=" + ec.message());
    }

    std::sort(sounds.begin(), sounds.end());

    bool selected_name_valid = IsSafeSoundName(selected_name);
    if (selected_name_valid) {
        selected_name_valid = std::find(sounds.begin(), sounds.end(), selected_name) != sounds.end();
    }
    if (!selected_name_valid && !selected_name.empty()) {
        selected_name.clear();
        std::ofstream selected_file(selected_path, std::ios::out | std::ios::trunc);
        if (!selected_file.is_open()) {
            logger_.Warn("webd", "failed to clear invalid selected sound file: " + selected_path +
                                     " error=" + std::strerror(errno));
        }
    }

    response.status = 200;
    response.body = "{";
    response.body += "\"selected_sound\":" + JsonString(selected_name) + ",";
    response.body += "\"sounds\":[";
    for (std::size_t i = 0; i < sounds.size(); ++i) {
        if (i > 0) {
            response.body += ",";
        }
        response.body += JsonString(sounds[i]);
    }
    response.body += "]}";
    return response;
}

WebServer::HttpResponse WebServer::HandleUploadRingSound(const HttpRequest &request) {
    HttpResponse response;

    const std::string prefix = "/api/v1/ring/sounds/";
    const std::string sound_name = request.path.substr(prefix.size());
    if (!IsSafeSoundName(sound_name)) {
        response.status = 400;
        response.body = "{\"error\":\"invalid_sound_name\",\"message\":\"Use ring-*.wav\"}";
        return response;
    }
    if (request.has_content_type) {
        const std::string mime_type = MimeTypeOnly(request.content_type);
        if (mime_type != "audio/wav" && mime_type != "audio/x-wav") {
            response.status = 415;
            response.body = "{\"error\":\"invalid_payload\",\"message\":\"payload is not a WAV file\"}";
            return response;
        }
    }

    if (request.body.size() < 12 || request.body.rfind("RIFF", 0) != 0 || request.body.compare(8, 4, "WAVE") != 0) {
        response.status = 415;
        response.body = "{\"error\":\"invalid_payload\",\"message\":\"payload is not a WAV file\"}";
        return response;
    }

    std::string ensure_error;
    if (!EnsureDirectoryExists(ring_sounds_dir_, &ensure_error)) {
        response.status = 500;
        response.body = "{\"error\":\"ring_sounds_unavailable\",\"message\":" + JsonString(ensure_error) + "}";
        return response;
    }

    const std::filesystem::path sound_path = std::filesystem::path(ring_sounds_dir_) / sound_name;
    const std::filesystem::path temp_path = sound_path.string() + ".tmp";

    {
        std::ofstream output(temp_path, std::ios::binary | std::ios::trunc);
        if (!output.is_open()) {
            response.status = 500;
            response.body = "{\"error\":\"save_failed\",\"message\":\"failed to open destination\"}";
            return response;
        }
        output.write(request.body.data(), static_cast<std::streamsize>(request.body.size()));
        output.flush();
        if (!output.good()) {
            output.close();
            std::error_code remove_ec;
            std::filesystem::remove(temp_path, remove_ec);
            response.status = 500;
            response.body = "{\"error\":\"save_failed\",\"message\":\"failed to write destination\"}";
            return response;
        }
    }

    std::error_code rename_ec;
    std::filesystem::rename(temp_path, sound_path, rename_ec);
    if (rename_ec) {
        std::error_code remove_ec;
        std::filesystem::remove(temp_path, remove_ec);
        response.status = 500;
        response.body = "{\"error\":\"save_failed\",\"message\":\"failed to move destination\"}";
        return response;
    }

    response.status = 200;
    response.body = "{\"uploaded\":" + JsonString(sound_name) + "}";
    return response;
}

WebServer::HttpResponse WebServer::HandleSelectRingSound(const HttpRequest &request) {
    HttpResponse response;
    const JsonParseResult parsed = ParseJson(request.body);
    if (!parsed.success || parsed.value.type() != JsonValue::Type::kObject) {
        response.status = 400;
        response.body = "{\"error\":\"invalid_json\",\"message\":\"payload must be an object\"}";
        return response;
    }

    std::vector<ValidationError> parse_errors;
    const auto sound_name = ReadRequiredString(parsed.value, "name", &parse_errors);
    if (!parse_errors.empty() || !sound_name.has_value() || !IsSafeSoundName(*sound_name)) {
        response.status = 400;
        response.body = "{\"error\":\"invalid_sound_name\",\"message\":\"Use ring-*.wav\"}";
        return response;
    }

    std::string ensure_error;
    if (!EnsureDirectoryExists(ring_sounds_dir_, &ensure_error)) {
        response.status = 500;
        response.body = "{\"error\":\"ring_sounds_unavailable\",\"message\":" + JsonString(ensure_error) + "}";
        return response;
    }

    const std::filesystem::path source = std::filesystem::path(ring_sounds_dir_) / *sound_name;
    if (!std::filesystem::exists(source) || !std::filesystem::is_regular_file(source)) {
        response.status = 404;
        response.body = "{\"error\":\"not_found\",\"message\":\"sound file does not exist\"}";
        return response;
    }

    const std::filesystem::path target_path(active_ring_sound_path_);
    std::error_code ec;
    std::filesystem::create_directories(target_path.parent_path(), ec);
    if (ec) {
        response.status = 500;
        response.body = "{\"error\":\"create_directory_failed\",\"message\":" +
                        JsonString("failed to create parent directory: " + ec.message()) + "}";
        return response;
    }

    const std::filesystem::path temp_path = target_path.string() + ".tmp";
    std::filesystem::copy_file(source, temp_path, std::filesystem::copy_options::overwrite_existing, ec);
    if (ec) {
        response.status = 500;
        response.body =
            "{\"error\":\"activate_failed\",\"message\":" + JsonString("failed to copy selected sound") + "}";
        return response;
    }

    std::filesystem::rename(temp_path, target_path, ec);
    if (ec) {
        std::filesystem::remove(temp_path, ec);
        response.status = 500;
        response.body =
            "{\"error\":\"activate_failed\",\"message\":" + JsonString("failed to activate selected sound") + "}";
        return response;
    }

    bool selection_persisted = true;
    {
        const std::string selected_path = ring_sounds_dir_ + "/selected.txt";
        const std::string temp_selected_path = selected_path + ".tmp";
        const std::string selected_value = *sound_name + "\n";

        int fd = open(temp_selected_path.c_str(), O_WRONLY | O_CREAT | O_TRUNC, 0644);
        if (fd < 0) {
            selection_persisted = false;
            logger_.Warn("webd", "failed to open selected file for write: " + temp_selected_path +
                                     " error=" + std::strerror(errno));
        } else {
            bool io_ok = true;
            const ssize_t written = write(fd, selected_value.data(), static_cast<size_t>(selected_value.size()));
            if (written != static_cast<ssize_t>(selected_value.size())) {
                io_ok = false;
            }
            if (io_ok && fsync(fd) != 0) {
                io_ok = false;
            }
            if (close(fd) != 0) {
                io_ok = false;
            }
            if (!io_ok) {
                selection_persisted = false;
                logger_.Warn("webd",
                             "failed to write selected file: " + temp_selected_path + " error=" + std::strerror(errno));
                std::remove(temp_selected_path.c_str());
            } else if (std::rename(temp_selected_path.c_str(), selected_path.c_str()) != 0) {
                selection_persisted = false;
                logger_.Warn("webd",
                             "failed to write selected file: " + selected_path + " error=" + std::strerror(errno));
                std::remove(temp_selected_path.c_str());
            }
        }
    }

    response.status = 200;
    response.body = "{\"selected\":" + JsonString(*sound_name) + ",";
    response.body += "\"selection_persisted\":" + JsonBool(selection_persisted);
    response.body += "}";
    return response;
}

std::optional<WebServer::HttpResponse> WebServer::TryServeExternalUi(const HttpRequest &request) const {
    if (ui_dist_dir_.empty() || request.method != "GET") {
        return std::nullopt;
    }
    if (request.path.empty() || request.path[0] != '/' || StartsWith(request.path, "/api/")) {
        return std::nullopt;
    }

    const std::filesystem::path root(ui_dist_dir_);
    std::error_code ec;
    if (!std::filesystem::exists(root, ec) || !std::filesystem::is_directory(root, ec)) {
        return std::nullopt;
    }

    auto response_from_file = [&](const std::filesystem::path &file_path,
                                  const std::string &request_path) -> std::optional<HttpResponse> {
        if (!std::filesystem::exists(file_path, ec) || !std::filesystem::is_regular_file(file_path, ec)) {
            return std::nullopt;
        }
        std::string body;
        if (!ReadFile(file_path, &body)) {
            HttpResponse response;
            response.status = 500;
            response.body = "{\"error\":\"ui_read_failed\"}";
            return response;
        }
        HttpResponse response;
        response.status = 200;
        response.content_type = ContentTypeForPath(file_path);
        response.cache_control = CacheControlForPath(request_path, file_path);
        response.body = std::move(body);
        return response;
    };

    if (request.path == "/") {
        const auto index_response = response_from_file(root / "index.html", "/");
        if (index_response.has_value()) {
            return index_response;
        }
        return std::nullopt;
    }

    const std::filesystem::path relative_path = std::filesystem::path(request.path).relative_path();
    if (relative_path.empty() || !IsSafeRelativePath(relative_path)) {
        HttpResponse response;
        response.status = 404;
        response.body = "{\"error\":\"not_found\"}";
        return response;
    }

    if (const auto file_response = response_from_file(root / relative_path, request.path); file_response.has_value()) {
        return file_response;
    }

    if (!StartsWith(request.path, "/assets/") && relative_path.extension().empty()) {
        if (const auto fallback_index = response_from_file(root / "index.html", "/"); fallback_index.has_value()) {
            return fallback_index;
        }
    }

    HttpResponse response;
    response.status = 404;
    response.body = "{\"error\":\"not_found\"}";
    return response;
}

WebServer::HttpResponse WebServer::ReservedNotImplemented(const std::string &path) const {
    HttpResponse response;
    response.status = 501;
    response.body = "{";
    response.body += "\"error\":\"not_implemented\",";
    response.body += "\"message\":\"reserved endpoint\",";
    response.body += "\"path\":" + JsonString(path);
    response.body += "}";
    return response;
}

bool WebServer::EnsureTlsMaterial(std::string *error) const {
    const bool cert_exists = std::filesystem::exists(cert_path_);
    const bool key_exists = std::filesystem::exists(key_path_);
    if (cert_exists && key_exists) {
        return true;
    }

    std::error_code ec;
    std::filesystem::create_directories(std::filesystem::path(cert_path_).parent_path(), ec);
    if (ec) {
        if (error != nullptr) {
            *error = "failed to create cert directory: " + ec.message();
        }
        return false;
    }

    std::filesystem::create_directories(std::filesystem::path(key_path_).parent_path(), ec);
    if (ec) {
        if (error != nullptr) {
            *error = "failed to create key directory: " + ec.message();
        }
        return false;
    }

    return GenerateSelfSignedCertificate(cert_path_, key_path_, error);
}

} // namespace chime::webd
